MOSH-Insa-Toulouse/2023-2024_4GP_NGO-TRAN/Image/LTspice/schema_suggere.png

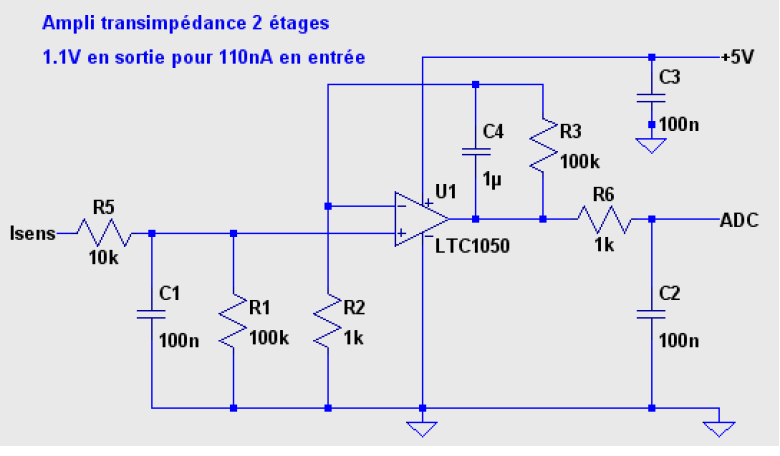
Image/LTspice/schema_suggere.png
