MOSH-Insa-Toulouse/2023-2024_4GP_NGO-TRAN/KICAD/oled-64x48-display-module-mdob064048av-wi-1.snapshot.1/OLED 64x48 Display Module - MDOB064048AV-WI/Renderings/Front.png

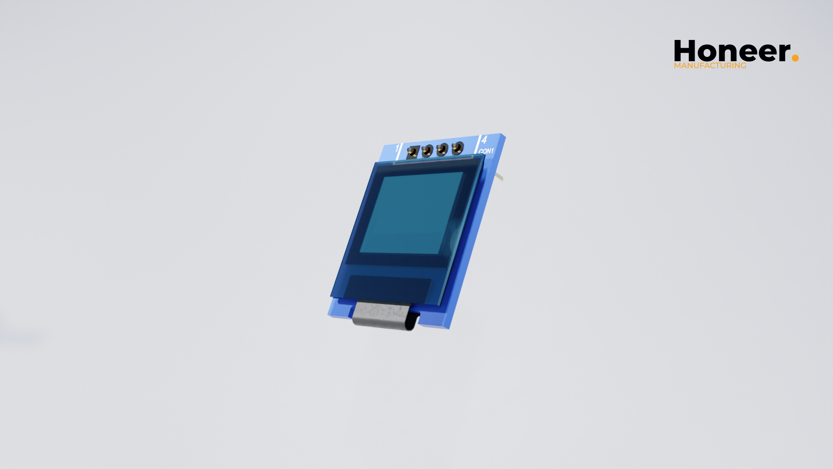
KICAD/oled-64x48-display-module-mdob064048av-wi-1.snapshot.1/OLED 64x48 Display Module - MDOB064048AV-WI/Renderings/Front.png
