MOSH-Insa-Toulouse/2023-2024_4GP_NGO-TRAN/KICAD/rotary-encoder-1.snapshot.8/Rotary Encoder/rotary encoder_chesr_2013.jpg

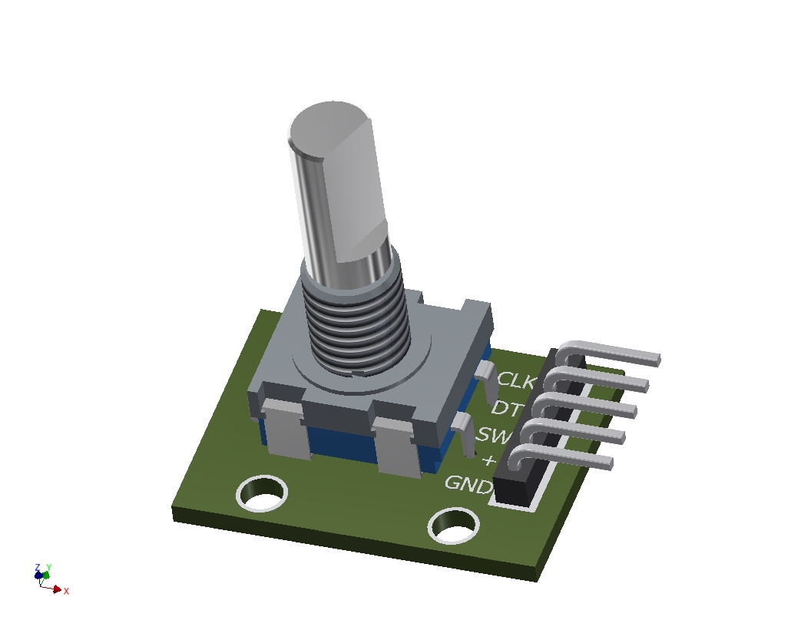
KICAD/rotary-encoder-1.snapshot.8/Rotary Encoder/rotary encoder_chesr_2013.jpg
