MOSH-Insa-Toulouse/2023-2024_4GP_NGO-TRAN/KICAD/rotary-encoder-1.snapshot.8/rotary encoder step files/Step Files/90d pin_header.stp

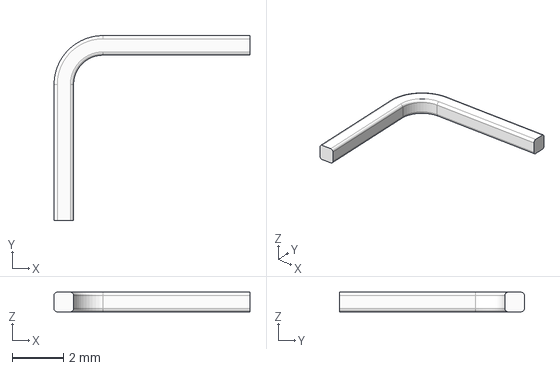
[picture p44: CAD file, 2024-04-23]
KICAD/rotary-encoder-1.snapshot.8/rotary encoder step files/Step Files/90d pin_header.stp
7.62 x 7.19 x 0.762 mm
