MOSH-Insa-Toulouse/2023-2024_4GP_NGO-TRAN/KICAD/rotary-encoder-1.snapshot.8/rotary encoder step files/Step Files/pcb.stp

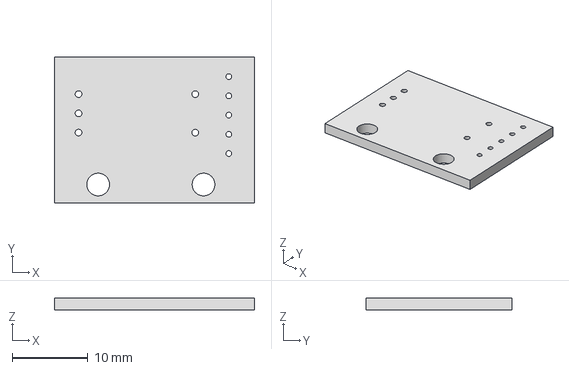
[picture p46: CAD file, 2024-04-23]
KICAD/rotary-encoder-1.snapshot.8/rotary encoder step files/Step Files/pcb.stp
26.4 x 19.3 x 1.52 mm
