MOSH-Insa-Toulouse/2023-2024_4GP_NGO-TRAN/KICAD/MCP41050_E_P(1)/MCP41050-E_P.step

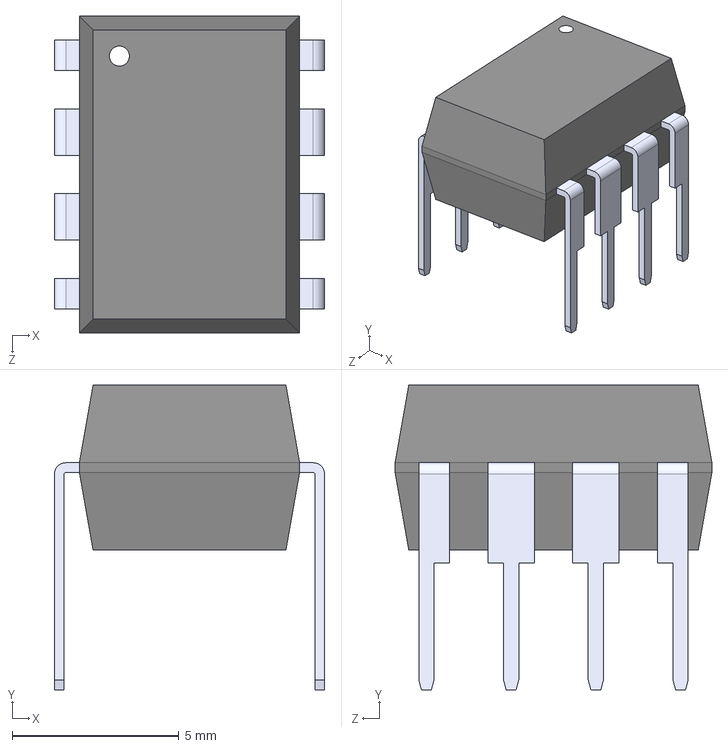
[picture p47: CAD file, 2024-04-23]
KICAD/MCP41050_E_P(1)/MCP41050-E_P.step
8.10 x 9.14 x 9.50 mm
